SartoriDynamics/Self-Balancing-Bike/3D printing/wheel_spacer.stl

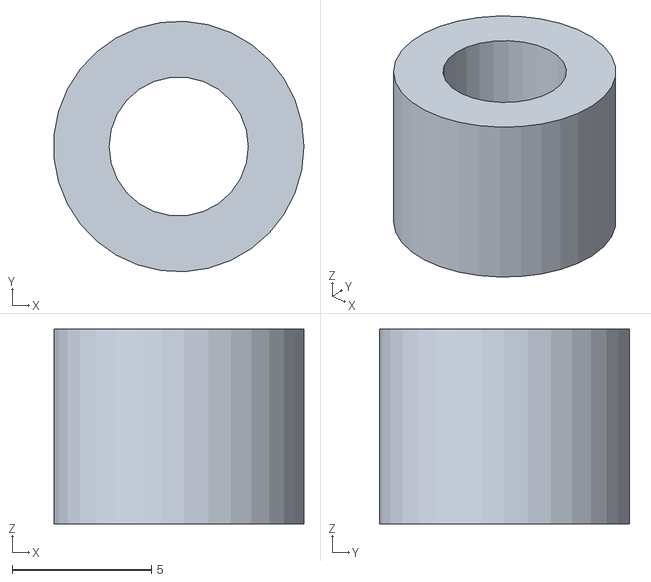
[picture p19: CAD file, 2025-03-11]
3D printing/wheel_spacer.stl
8.98 x 8.99 x 7.00
