SartoriDynamics/Self-Balancing-Bike/3D printing/flywheel.stl

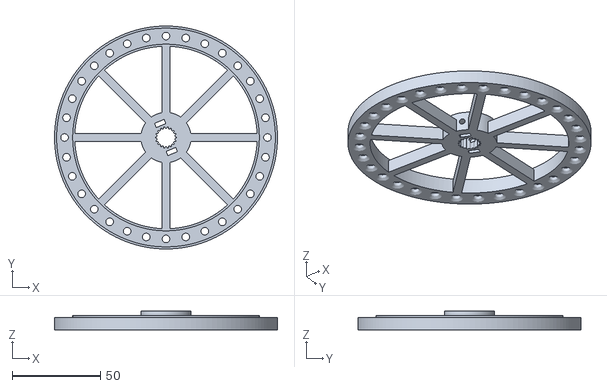
[picture p20: CAD file, 2025-03-11]
3D printing/flywheel.stl
126.4 x 126.4 x 10.5
