SartoriDynamics/Self-Balancing-Bike/3D printing/right_body.stl

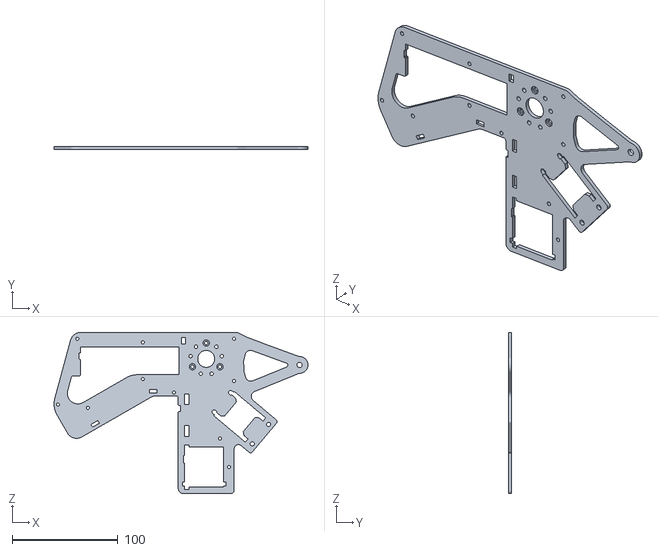
[picture p21: CAD file, 2025-03-11]
3D printing/right_body.stl
240.4 x 3.00 x 152.5
