SartoriDynamics/Self-Balancing-Bike/3D printing/wheel_gear.stl

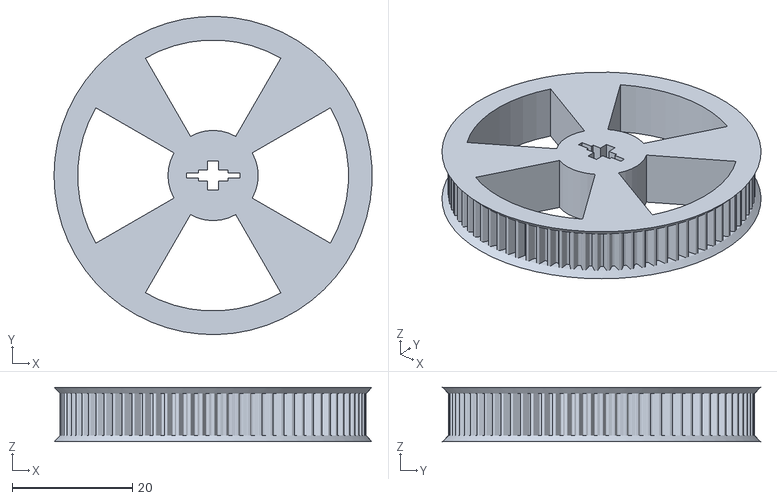
[picture p22: CAD file, 2025-03-11]
3D printing/wheel_gear.stl
52.8 x 52.8 x 9.00
