SartoriDynamics/Self-Balancing-Bike/3D printing/fork.stl

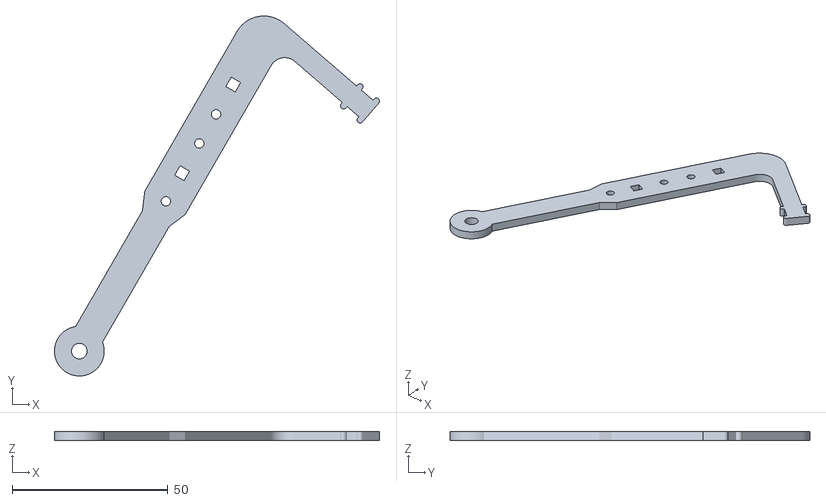
[picture p23: CAD file, 2025-03-11]
3D printing/fork.stl
104.5 x 115.8 x 3.00
