SartoriDynamics/Self-Balancing-Bike/3D printing/Nidec_holder.stl

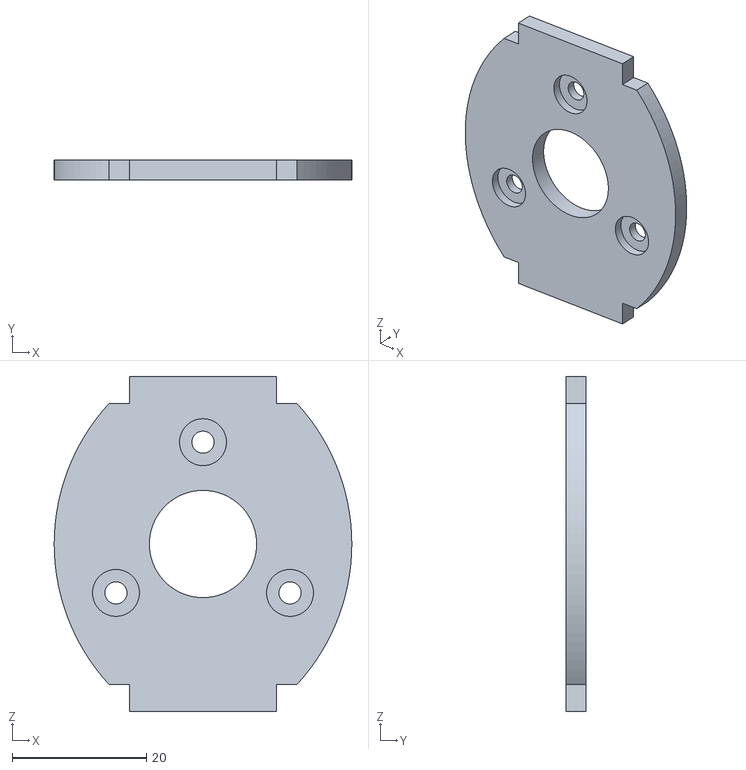
[picture p24: CAD file, 2025-03-11]
3D printing/Nidec_holder.stl
44.4 x 3.00 x 50.0
