SartoriDynamics/Self-Balancing-Bike/3D printing/regulator_holder.stl

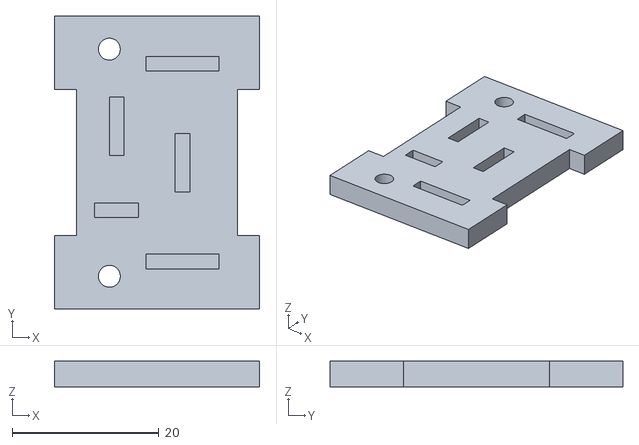
[picture p25: CAD file, 2025-03-11]
3D printing/regulator_holder.stl
28.0 x 40.0 x 3.50
